gatechipdl/GameOfLight/idea renders/hanging game of light_render-01.png

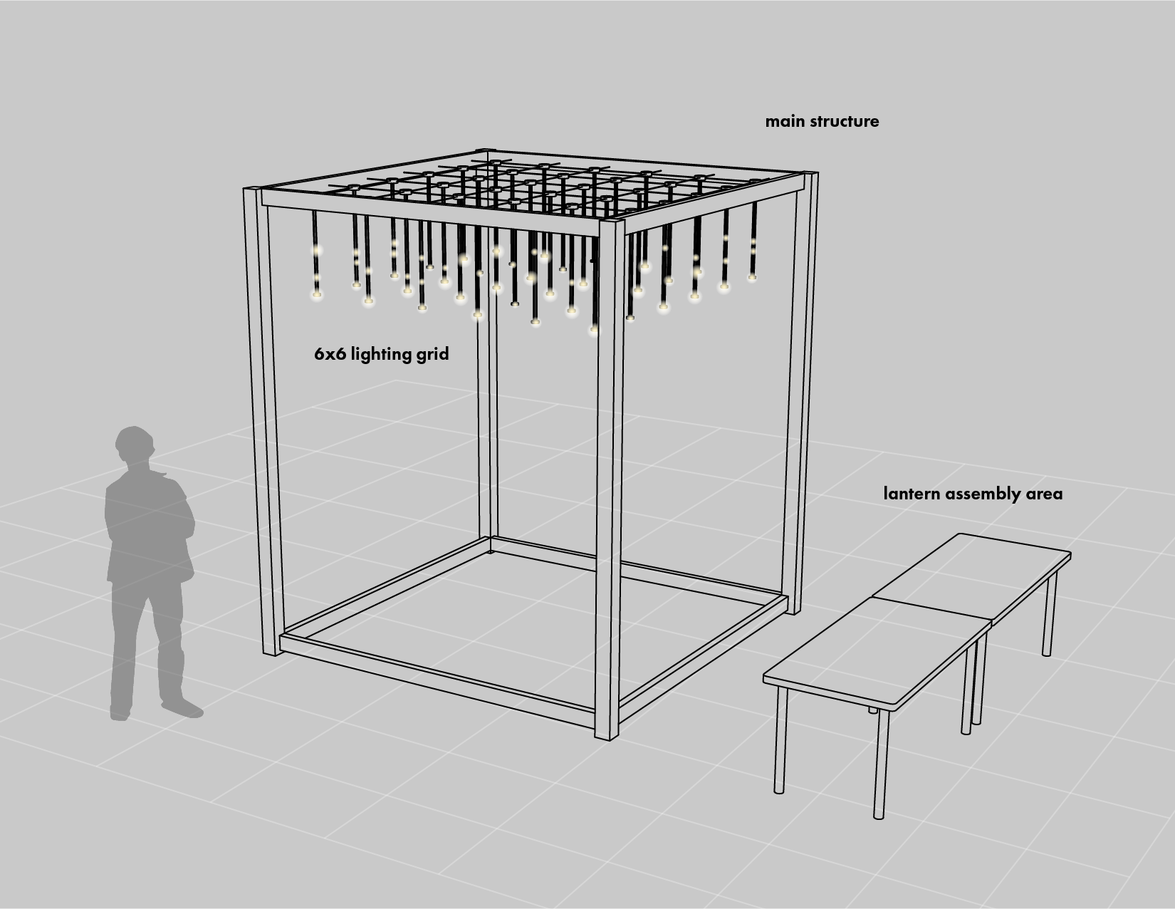
idea renders/hanging game of light_render-01.png
