gatechipdl/GameOfLight/idea renders/standing game of light_render-01.png

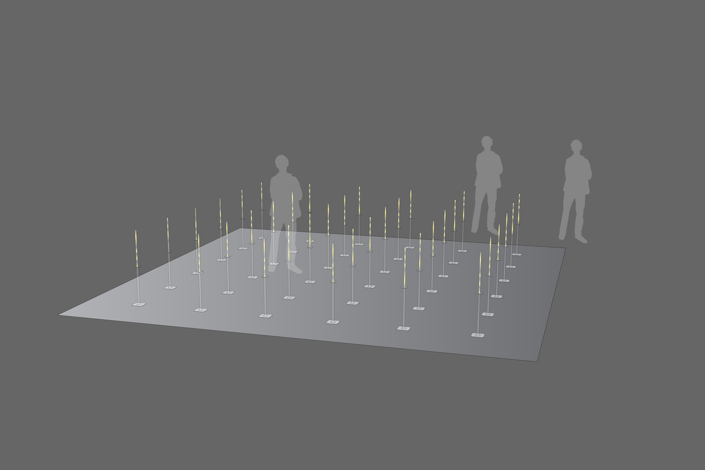
idea renders/standing game of light_render-01.png
