gatechipdl/GameOfLight/idea renders/standing game of light_render-03.png

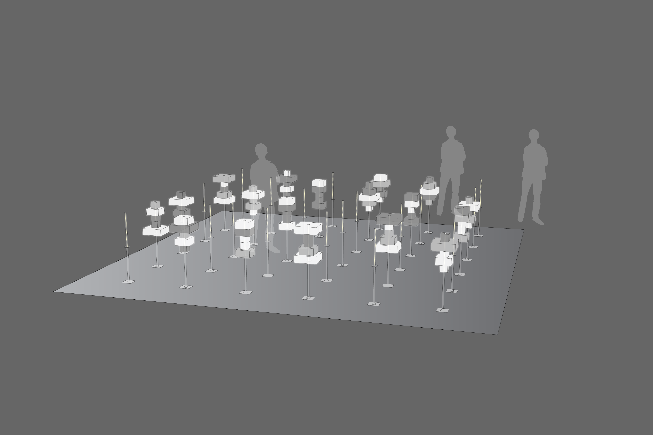
idea renders/standing game of light_render-03.png
