gatechipdl/GameOfLight/Solidworks/LampV1/LampBlock_V1_Hook.sldprt

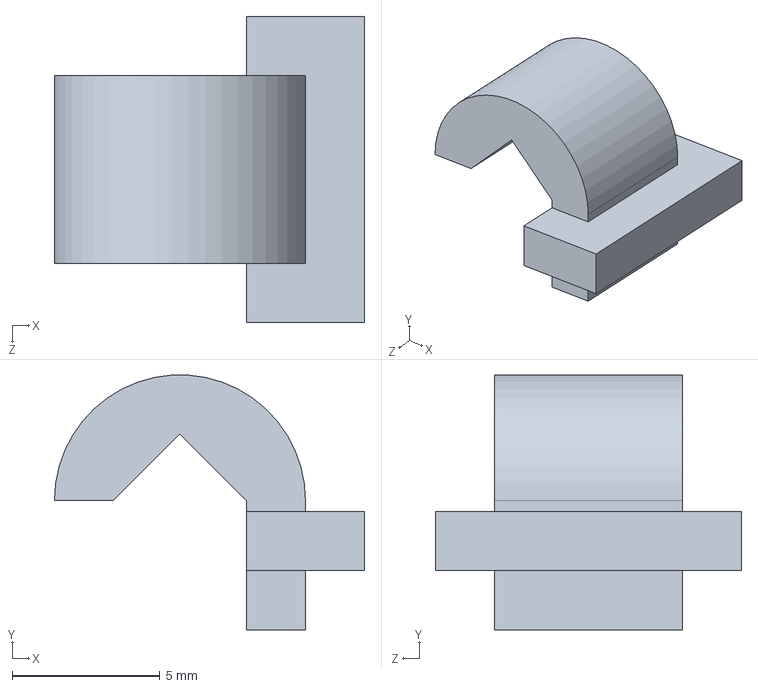
[picture p23: CAD file, 2017-03-27, an earlier design]
Solidworks/LampV1/LampBlock_V1_Hook.sldprt
10.5 x 8.62 x 10.4 mm
